eddypurplehorse/ECE411_Team_Game_Person/kicad_schematic/V2_LCD_GAME_PCB.png

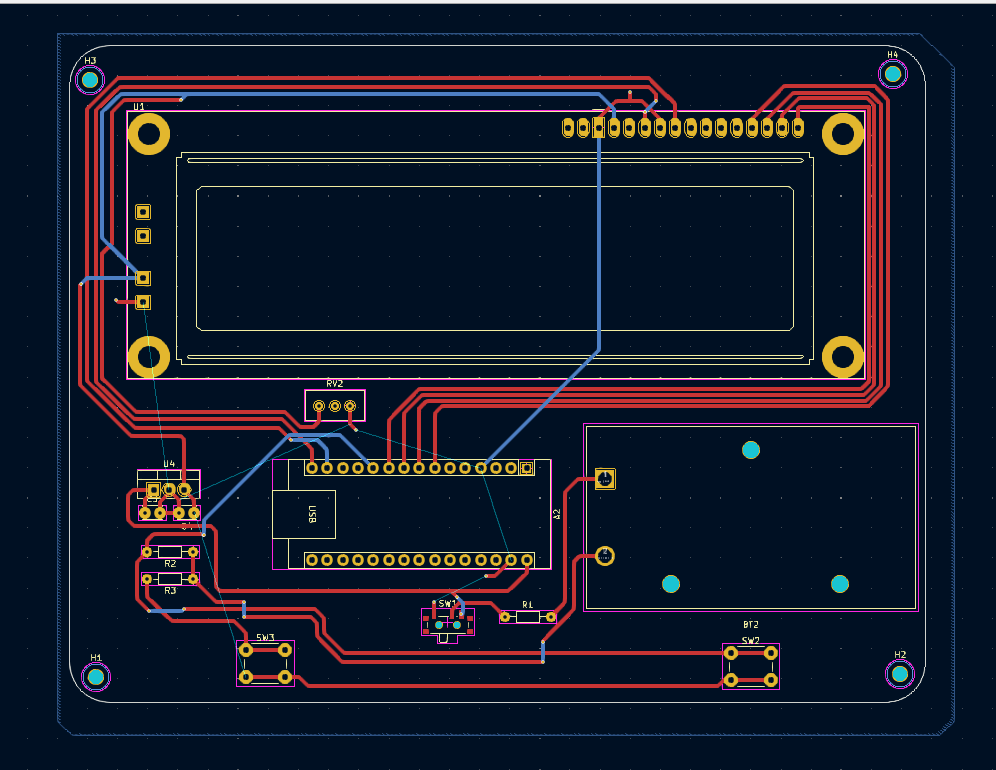
kicad_schematic/V2_LCD_GAME_PCB.png
