eddypurplehorse/ECE411_Team_Game_Person/kicad_schematic/V4_LCD_GAME_PCB_FINAL_VERSION.png

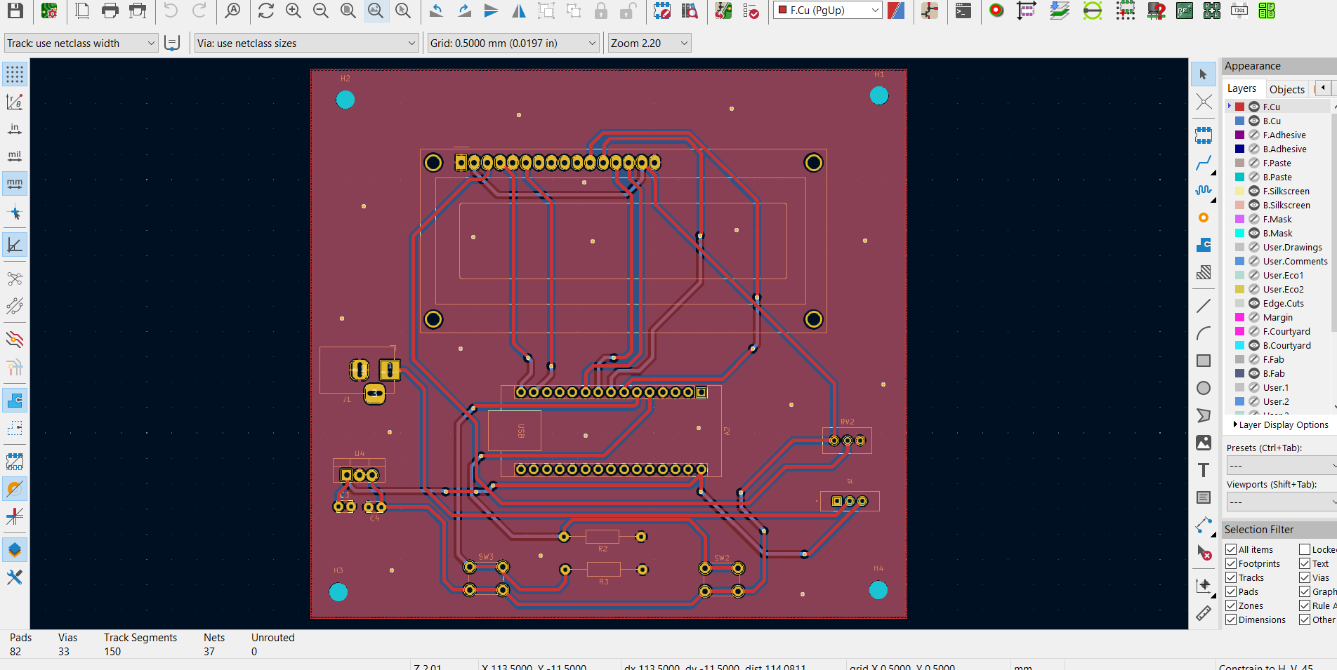
kicad_schematic/V4_LCD_GAME_PCB_FINAL_VERSION.png
