eddypurplehorse/ECE411_Team_Game_Person/photos/project_prototype.jpg

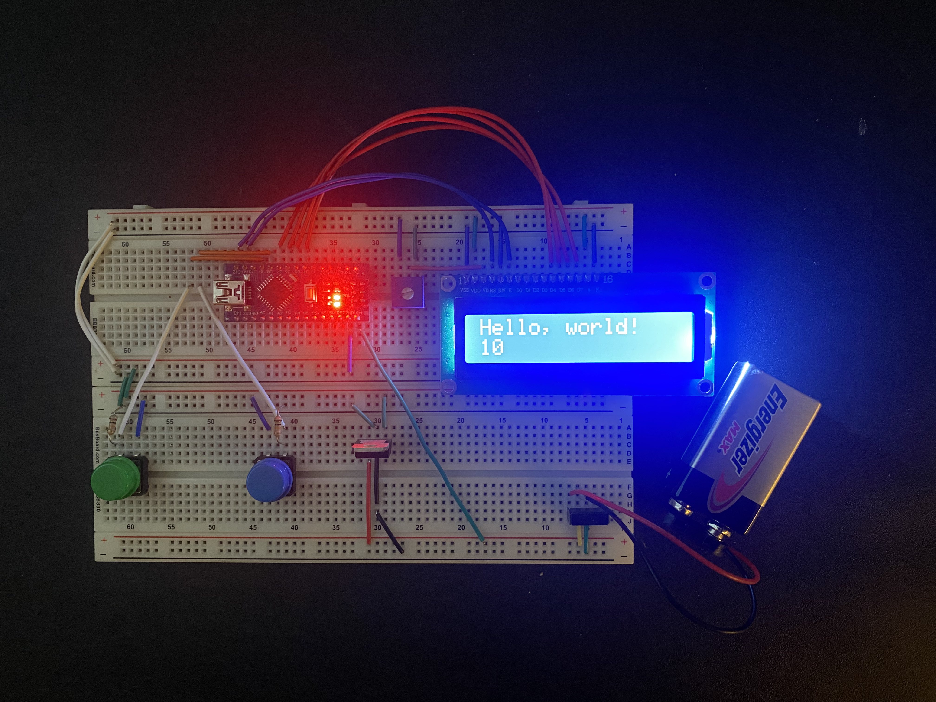
photos/project_prototype.jpg
