eddypurplehorse/ECE411_Team_Game_Person/photos/test1.jpg

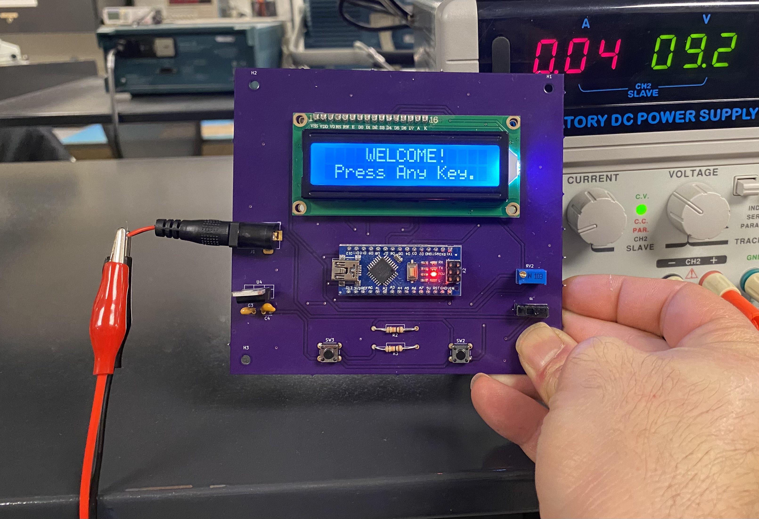
photos/test1.jpg
