eddypurplehorse/ECE411_Team_Game_Person/photos/test2.jpg

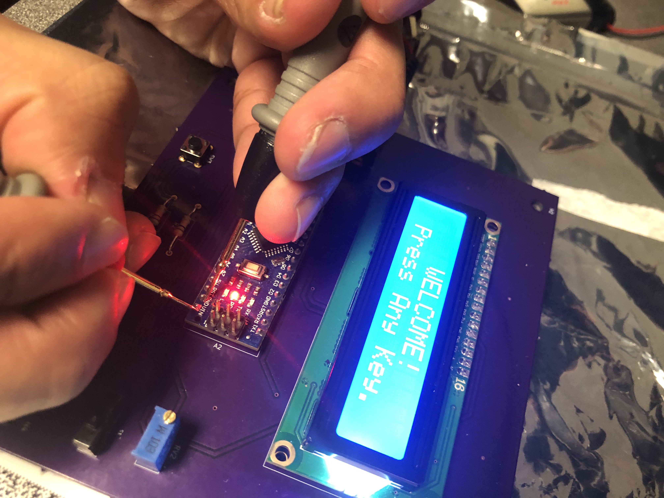
photos/test2.jpg
