eddypurplehorse/ECE411_Team_Game_Person/photos/test3.jpg

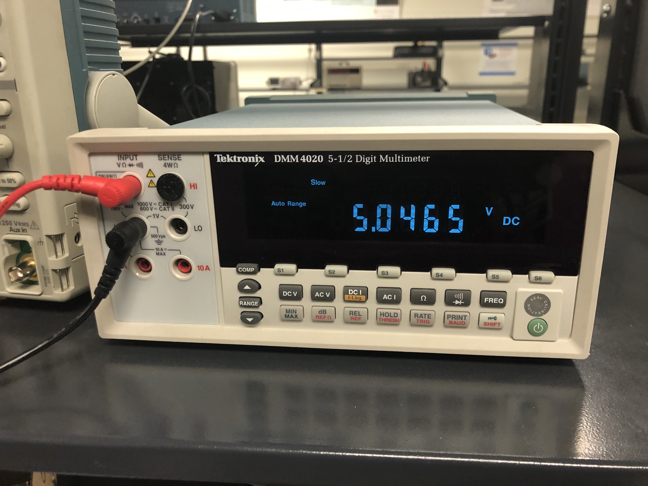
photos/test3.jpg
