eddypurplehorse/ECE411_Team_Game_Person/photos/test4.jpg

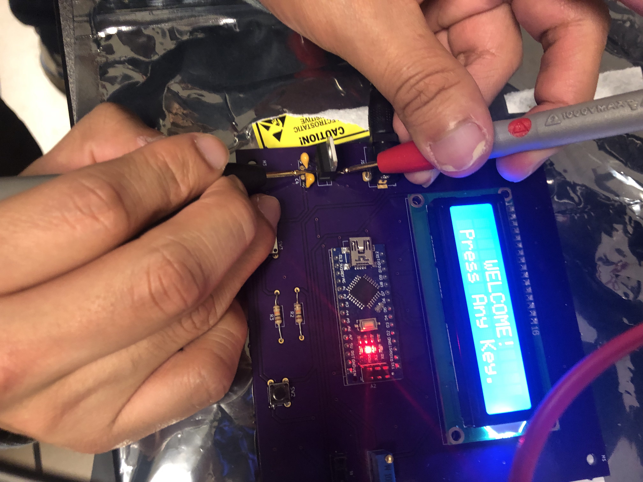
photos/test4.jpg
