eddypurplehorse/ECE411_Team_Game_Person/photos/test5.jpg

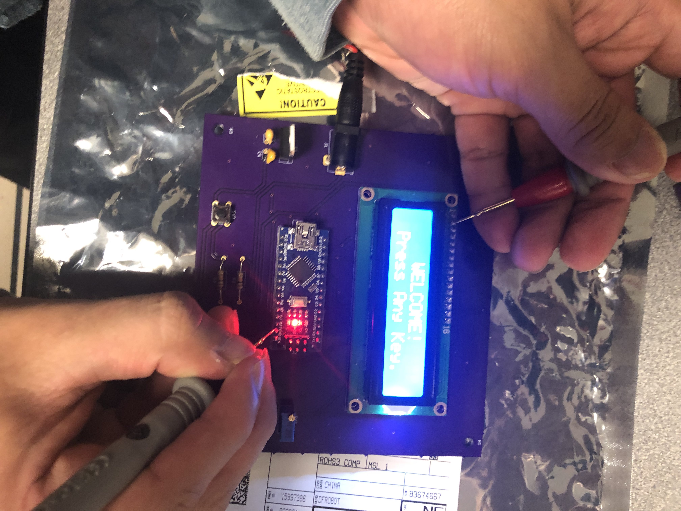
photos/test5.jpg
