eddypurplehorse/ECE411_Team_Game_Person/photos/Test_0.jpg

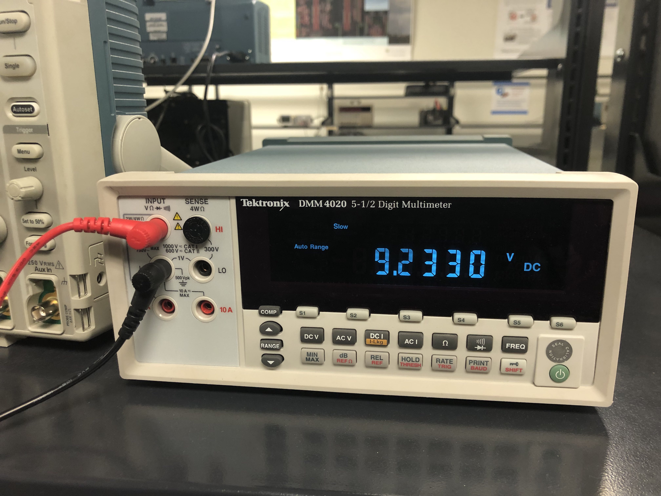
photos/Test_0.jpg
